alvaroalea/QL_qplane/pics/from.jpg

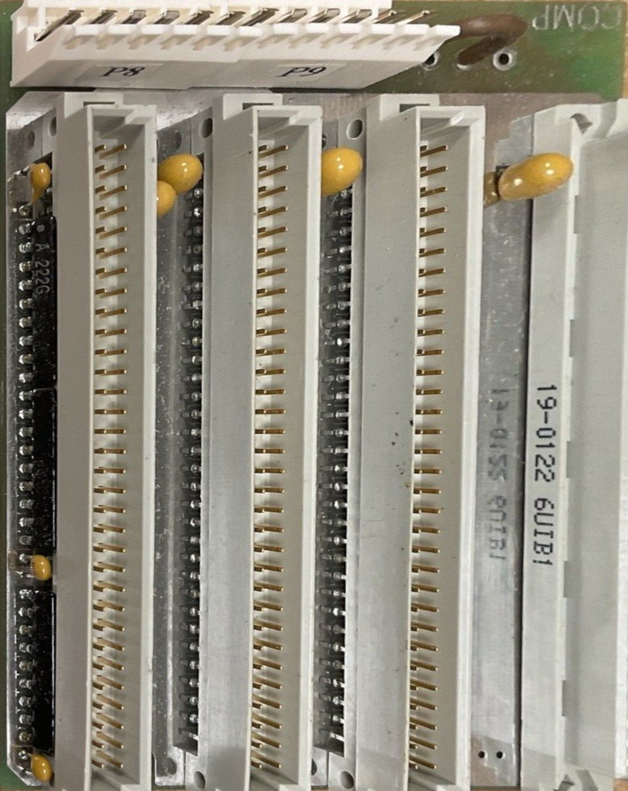
pics/from.jpg
