alvaroalea/QL_qplane/pics/front.jpg

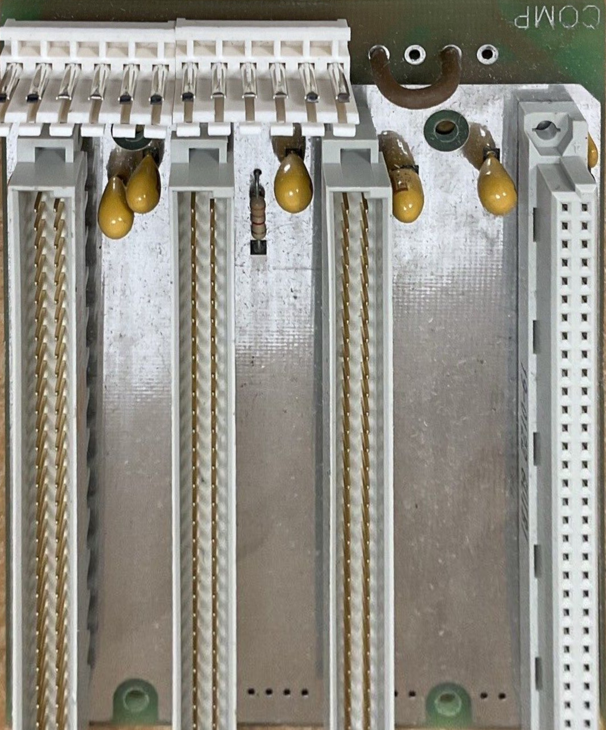
pics/front.jpg
