alvaroalea/QL_qplane/pics/Qplane1.jpg

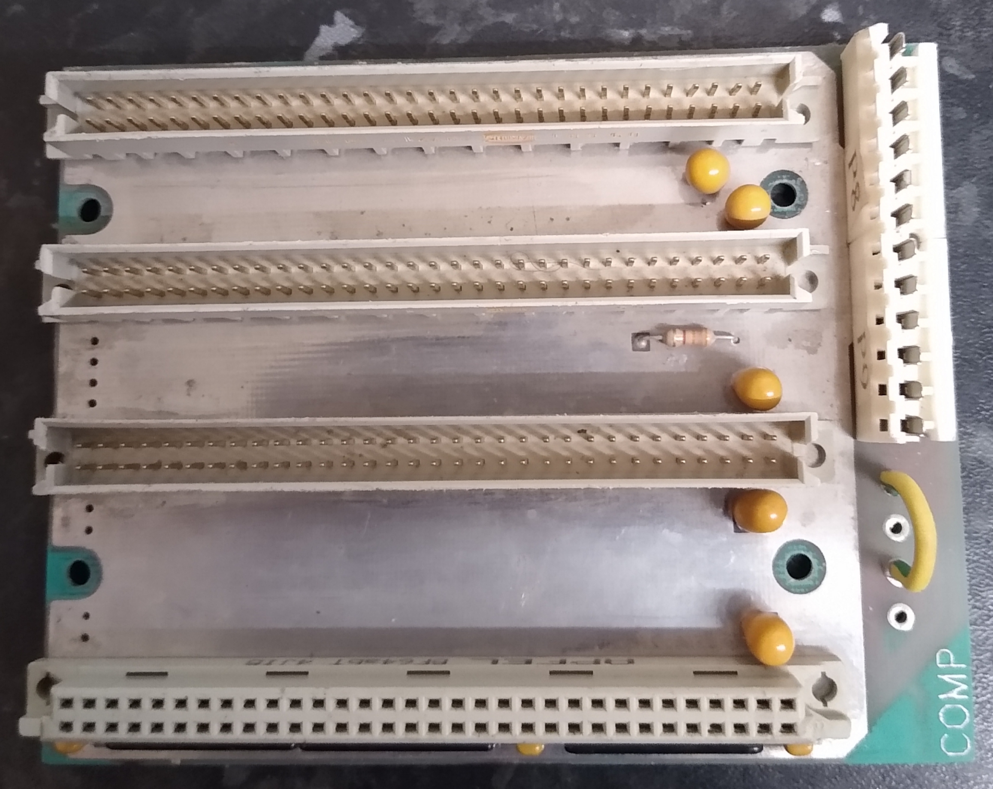
pics/Qplane1.jpg
