alvaroalea/QL_qplane/pics/s-l1600-2.jpg

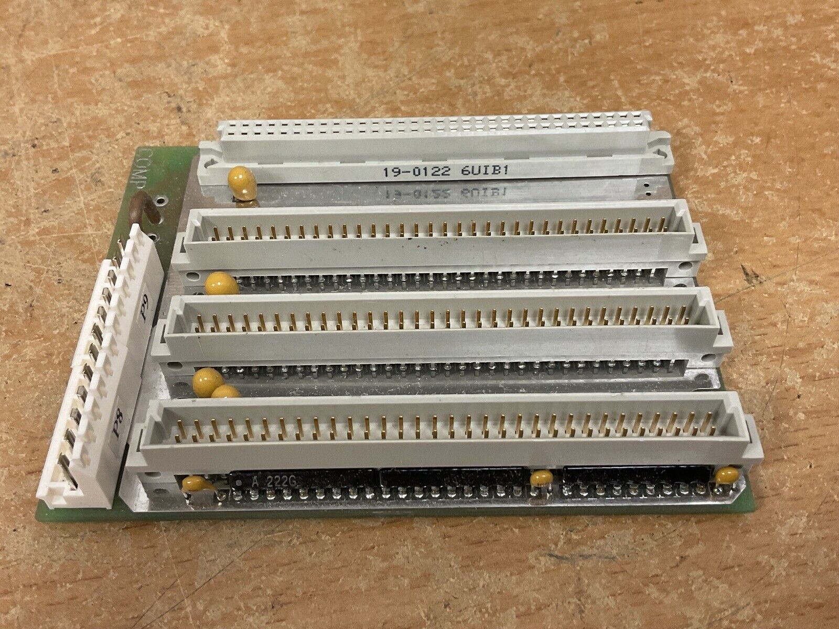
pics/s-l1600-2.jpg
