alvaroalea/QL_qplane/pics/s-l1600-4.jpg

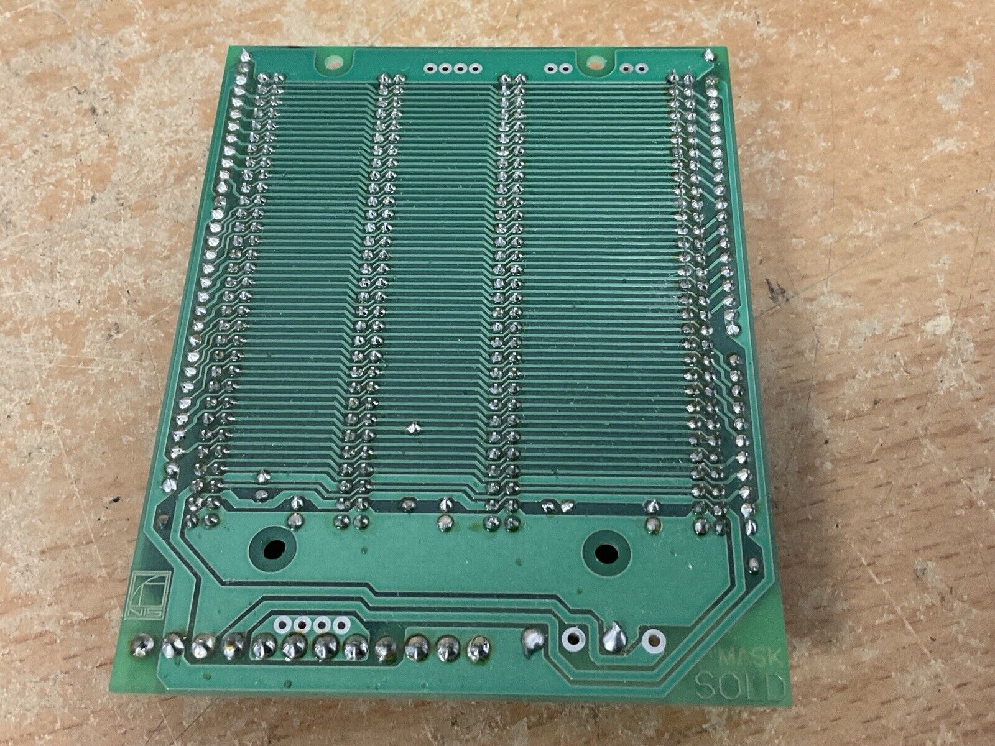
pics/s-l1600-4.jpg
