alvaroalea/QL_qplane/pics/s-l1600-6.jpg

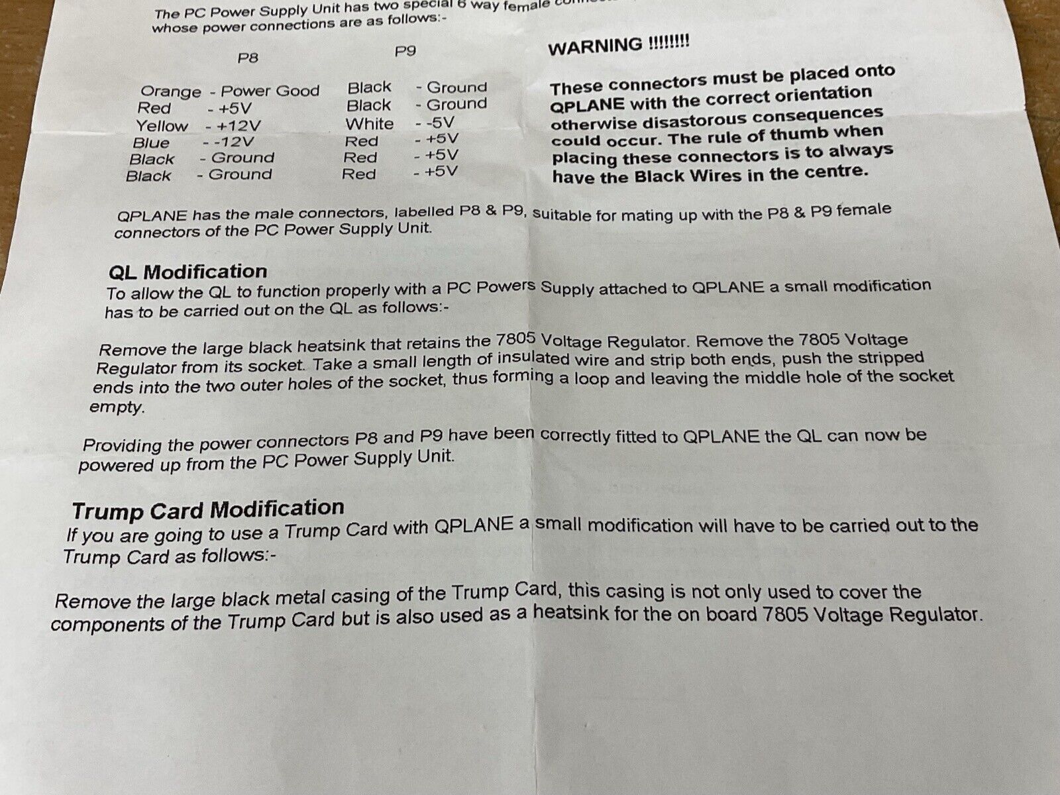
pics/s-l1600-6.jpg
