alvaroalea/QL_qplane/pics/s-l1600_1.jpg

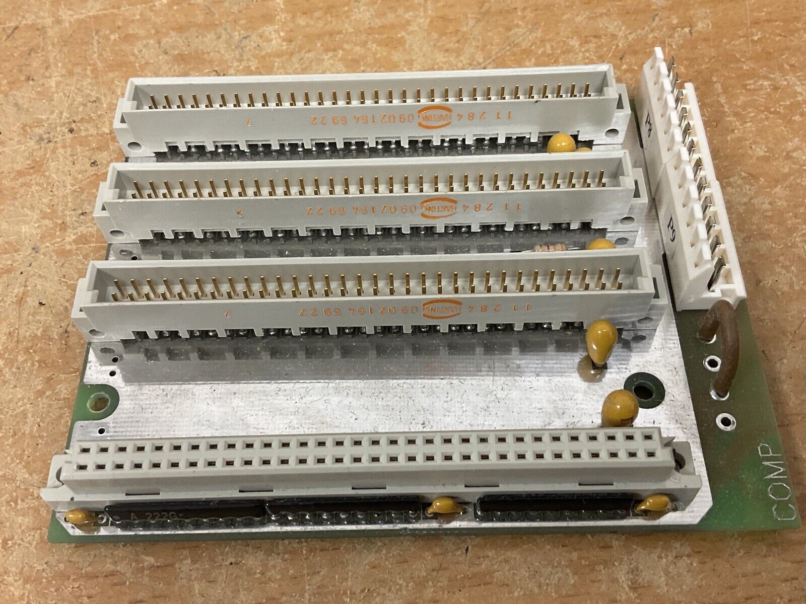
pics/s-l1600_1.jpg
